ilove737/XS16_CH552T/src/keyMap.h

#ifndef __KEY_MAP_H__
#define __KEY_MAP_H__

#include "CH552.H"
#include "scanKey.h"

// =========================================================================
// 应用场景（纯编号，不再预设语义 ID）
// 所有场景（含主层）统一放入一个大二维数组 sceneMapTable[SCENE_MAX][80]，
// 通过 currentScene 编号偏移定位。每槽 80 字节：
//   [0..15]   应用名称（ASCII，不足补 0，第 16 字节作 0 结尾，最多 15 字符）
//   [16..47]  主层键位（16 键 × 2）
//   [48..79]  该场景专属 Fn 层键位（16 键 × 2）
// =========================================================================
#define SCENE_MAX         6     // 场景槽位总数（编号 0~5）
#define NAME_SIZE         16    // 应用名区长度（字节）
#define KEY_BYTES         32    // 每层键位长度（16 键 × 2 字节）
#define SCENE_MAP_SIZE    80    // 每槽总长度 = NAME_SIZE + KEY_BYTES*2

// 各槽位在数组中的键位区偏移
#define MAP_MAIN_OFF      NAME_SIZE              // 16：主层键位起始
#define MAP_FN_OFF        (NAME_SIZE + KEY_BYTES) // 48：Fn 层键位起始

// 场景指令接收协议（经中断 OUT 端点 3，厂商自定义 Output 报告，Report ID = 2）
// 数据格式：[0]=ReportID(0x02) [1]=SCENE_CMD_MAGIC(0x5C) [2]=场景ID [3..7]=0
#define SCENE_CMD_MAGIC  0x5C

// =========================================================================
// 键位映射大二维数组（编译期固定，__at(0x3600)）
// 6 槽 × 80 字节 = 480 字节，占 0x3600 ~ 0x37DF。
// app 通过扩展后的 Feature Report 可读改写其中任意槽（含应用名与键位）。
// 通用主层键位（deepin 系统快捷键）与 Fn 键位见下方注释。
// =========================================================================
UINT8C __at(0x3600) sceneMapTable[SCENE_MAX][SCENE_MAP_SIZE] = {
    // ---- 槽 0：主层（编号 0，应用名 generic） ----
    {
        /* 应用名 0..15 */
        'g','e','n','e','r','i','c', 0,0,0,0,0,0,0,0,0,
        /* 主层键位 16..47（deepin 系统快捷键，按 keymap_XS16 导出） */
        KEY_MOD_LCTRL|KEY_MOD_LALT, KEY_LEFT,    // Ctrl+Alt+←  切换到左边工作区
        KEY_MOD_LMETA, KEY_S,                    // Win+S       显示工作区
        KEY_MOD_LSHIFT, KEY_SPACE,               // Shift+Space 全局搜索
        KEY_MOD_LCTRL|KEY_MOD_LALT, KEY_RIGHT,   // Ctrl+Alt+→  切换到右边工作区
        KEY_MOD_LALT, KEY_TAB,                   // Alt+Tab     切换窗口
        KEY_MOD_LALT, KEY_GRAVE,                 // Alt+`       切换同类型窗口
        KEY_MOD_LSHIFT|KEY_MOD_LALT, KEY_GRAVE,  // Shift+Alt+` 反向切换同类型窗口
        KEY_MOD_LSHIFT|KEY_MOD_LALT, KEY_TAB,    // Shift+Alt+Tab 反向切换窗口
        KEY_MOD_LALT, KEY_F2,                    // Alt+F2      终端雷神模式
        KEY_MOD_LMETA, KEY_N,                    // Win+N       最小化窗口
        KEY_MOD_LMETA, KEY_UP,                   // Win+↑       最大化窗口
        KEY_MOD_LMETA, KEY_V,                    // Win+V       剪贴板
        KEY_FnX, 0,                              // Fn          切换 Fn 层
        KEY_MOD_LMETA, KEY_LEFT,                 // Win+←       窗口平铺左侧
        KEY_MOD_LMETA, KEY_DOWN,                 // Win+↓       恢复窗口
        KEY_MOD_LMETA, KEY_RIGHT,                // Win+→       窗口平铺右侧
        /* Fn 层键位 48..79（deepin 截图/录屏/图文识别 + 鼠标，按 keymap_XS16 导出） */
        KEY_MOD_LCTRL|KEY_MOD_LALT, KEY_I,       // Ctrl+Alt+I  滚动截图
        KEY_MOD_LCTRL|KEY_MOD_LALT, KEY_A,       // Ctrl+Alt+A  截图
        KEY_MOD_LCTRL, KEY_SYSRQ,                // Ctrl+PrtSc  延时截图
        0, KEY_SYSRQ,                            // PrtSc       全屏截图
        KEY_MOD_LALT, KEY_SYSRQ,                 // Alt+PrtSc   窗口截图
        KEY_MOD_LCTRL|KEY_MOD_LALT, KEY_C,       // Ctrl+Alt+C  图文识别
        KEY_MOD_LCTRL|KEY_MOD_LALT, KEY_R,       // Ctrl+Alt+R  录屏
        KEY_MOD_LMETA, KEY_E,                    // Win+E       文件管理器
        KEY_MOD_LMETA, 0,                        // Win+空      启动器(占位)
        0xFE, MOUSE_LCLICK, 0xFE, MOUSE_UP, 0xFE, MOUSE_RCLICK,
        KEY_FnX, 0,  0xFE, MOUSE_LEFT, 0xFE, MOUSE_DOWN, 0xFE, MOUSE_RIGHT,
    },
    // ---- 槽 1：场景 1（编号 1，应用名 deepin-terminal，终端定制键位） ----
    {
        /* 应用名 0..15 */
        'd','e','e','p','i','n','-','t','e','r','m', 'i','n','a','l',0,
        /* 主层键位 16..47（终端定制，按 keymap_XS16 导出） */
        KEY_MOD_LCTRL|KEY_MOD_LSHIFT, KEY_1,   // Ctrl+Shift+1 切换到标签1
        KEY_MOD_LCTRL|KEY_MOD_LSHIFT, KEY_2,   // Ctrl+Shift+2 切换到标签2
        KEY_MOD_LCTRL, KEY_EQUAL,              // Ctrl+=       放大字号
        KEY_MOD_LCTRL, KEY_MINUS,              // Ctrl+-       缩小字号
        KEY_MOD_LCTRL|KEY_MOD_LSHIFT, KEY_T,   // Ctrl+Shift+T 新建标签页
        KEY_MOD_LCTRL|KEY_MOD_LSHIFT, KEY_TAB, // Ctrl+Shift+Tab 上一个标签页
        KEY_MOD_LCTRL, KEY_TAB,                // Ctrl+Tab     下一个标签页
        KEY_MOD_LALT, KEY_W,                   // Alt+W        关闭标签页
        KEY_MOD_LCTRL|KEY_MOD_LSHIFT, KEY_C,   // Ctrl+Shift+C 复制
        KEY_MOD_LCTRL|KEY_MOD_LSHIFT, KEY_V,   // Ctrl+Shift+V 粘贴
        KEY_MOD_LALT, KEY_DOWN,                // Alt+↓        选择下面工作区
        KEY_MOD_LALT, KEY_Q,                   // Alt+Q        关闭工作区
        KEY_FnX, 0,                            // Fn           切换 Fn 层
        KEY_MOD_LALT, KEY_LEFT,                // Alt+←        选择左边工作区
        KEY_MOD_LALT, KEY_UP,                  // Alt+↑        选择上面工作区
        KEY_MOD_LALT, KEY_RIGHT,               // Alt+→        选择右边工作区
        /* Fn 层键位 48..79（终端分屏/查找/全选 + 鼠标，按 keymap_XS16 导出） */
        KEY_MOD_LCTRL|KEY_MOD_LSHIFT, KEY_J,   // Ctrl+Shift+J 纵向分屏
        KEY_MOD_LCTRL|KEY_MOD_LSHIFT, KEY_H,   // Ctrl+Shift+H 横向分屏
        KEY_MOD_LCTRL|KEY_MOD_LALT, KEY_F,     // Ctrl+Alt+F   查找
        KEY_MOD_LCTRL, KEY_0,                  // Ctrl+0       默认大小
        KEY_MOD_LCTRL|KEY_MOD_LSHIFT, KEY_A,   // Ctrl+Shift+A 全选
        0, KEY_F11,                            // F11          全屏
        KEY_MOD_LCTRL|KEY_MOD_LSHIFT, KEY_W,   // Ctrl+Shift+W 关闭其他标签页
        KEY_MOD_LCTRL|KEY_MOD_LSHIFT, KEY_Q,   // Ctrl+Shift+Q 关闭其他工作区
        0, KEY_F2,                             // F2           重命名标题
        0xFE, MOUSE_LCLICK, 0xFE, MOUSE_UP, 0xFE, MOUSE_RCLICK,
        KEY_FnX, 0,  0xFE, MOUSE_LEFT, 0xFE, MOUSE_DOWN, 0xFE, MOUSE_RIGHT,
    },
    // ---- 槽 2：场景 2（编号 2，应用名 code，VS Code 定制键位） ----
    {
        /* 应用名 0..15 */
        'c','o','d','e', 0,0,0,0,0,0,0,0,0,0,0,0,
        /* 主层键位 16..47（VS Code 编辑优先） */
        KEY_MOD_LCTRL|KEY_MOD_LSHIFT, KEY_P,      // Ctrl+Shift+P   命令面板
        KEY_MOD_LCTRL, KEY_P,                     // Ctrl+P         快速打开文件
        KEY_MOD_LCTRL, KEY_S,                     // Ctrl+S         保存
        KEY_MOD_LCTRL, KEY_GRAVE,                 // Ctrl+`         集成终端
        KEY_MOD_LCTRL, KEY_RIGHTBRACE,            // Ctrl+]         缩进
        KEY_MOD_LCTRL, KEY_LEFTBRACE,             // Ctrl+[         反缩进
        KEY_MOD_LSHIFT|KEY_MOD_LALT, KEY_DOWN,    // Shift+Alt+↓    向下插入光标（列编辑）
        KEY_MOD_LSHIFT|KEY_MOD_LALT, KEY_UP,      // Shift+Alt+↑    向上插入光标（列编辑）
        KEY_MOD_LALT, KEY_DOWN,                   // Alt+↓          下移行
        KEY_MOD_LALT, KEY_UP,                     // Alt+↑          上移行
        KEY_MOD_LCTRL, KEY_D,                     // Ctrl+D         选中下一个匹配
        KEY_MOD_LCTRL|KEY_MOD_LSHIFT, KEY_L,      // Ctrl+Shift+L   全选匹配
        KEY_FnX, 0,                               // Fn             切换 Fn 层
        KEY_MOD_LCTRL, KEY_SLASH,                 // Ctrl+/         行注释
        KEY_MOD_LCTRL|KEY_MOD_LSHIFT, KEY_K,      // Ctrl+Shift+K   删除行
        KEY_MOD_LCTRL, KEY_ENTER,                 // Ctrl+Enter     下方插入行
        /* Fn 层键位 48..79（调试/重构/查找 + 鼠标） */
        0, KEY_F5,                                // F5             启动/继续调试
        0, KEY_F9,                                // F9             切换断点
        0, KEY_F12,                               // F12            转到定义
        0, KEY_F2,                                // F2             重命名符号
        0, KEY_F8,                                // F8             下一个错误
        KEY_MOD_LCTRL, KEY_DOT,                   // Ctrl+.         快速修复
        KEY_MOD_LCTRL|KEY_MOD_LSHIFT, KEY_ENTER,  // Ctrl+Shift+Enter 上方插入行
        KEY_MOD_LCTRL, KEY_F,                     // Ctrl+F         查找
        KEY_MOD_LCTRL, KEY_H,                     // Ctrl+H         替换
        0xFE, MOUSE_LCLICK, 0xFE, MOUSE_UP, 0xFE, MOUSE_RCLICK,
        KEY_FnX, 0,  0xFE, MOUSE_LEFT, 0xFE, MOUSE_DOWN, 0xFE, MOUSE_RIGHT,
    },
    // ---- 槽 3：场景 3（编号 3，应用名 dde-file-manager，deepin 文件管理器定制键位） ----
    {
        /* 应用名 0..15 */
        'f','i','l','e','-','m','a','n','a','g','e','r', 0,0,0,0,
        /* 主层键位 16..47（文件管理器高频操作，按 DEEPIN_FILEMANAGER_SHORTCUTS 挑选） */
        KEY_MOD_LCTRL, KEY_N,                  // Ctrl+N         新建窗口
        KEY_MOD_LCTRL|KEY_MOD_LSHIFT, KEY_N,   // Ctrl+Shift+N   新建文件夹
        KEY_MOD_LCTRL, KEY_T,                  // Ctrl+T         新建标签
        KEY_MOD_LCTRL, KEY_W,                  // Ctrl+W         关闭当前标签
        KEY_MOD_LCTRL, KEY_F,                  // Ctrl+F         搜索
        KEY_MOD_LCTRL, KEY_L,                  // Ctrl+L         地址栏输入
        KEY_MOD_LALT, KEY_LEFT,                // Alt+←          后退
        KEY_MOD_LALT, KEY_RIGHT,               // Alt+→          前进
        KEY_MOD_LCTRL, KEY_UP,                 // Ctrl+↑         返回上一级
        KEY_MOD_LCTRL, KEY_DOWN,               // Ctrl+↓         打开
        KEY_MOD_LCTRL, KEY_A,                  // Ctrl+A         全选
        KEY_MOD_LCTRL, KEY_TAB,                // Ctrl+Tab       切换到下一个标签
        KEY_FnX, 0,                            // Fn             切换 Fn 层
        KEY_MOD_LCTRL, KEY_C,                  // Ctrl+C         复制
        KEY_MOD_LCTRL, KEY_X,                  // Ctrl+X         剪切
        KEY_MOD_LCTRL, KEY_V,                  // Ctrl+V         粘贴
        /* Fn 层键位 48..79（重命名/删除/撤销 + 鼠标） */
        0, KEY_F2,                             // F2             重命名
        0, KEY_DELETE,                         // Delete         删除文件
        KEY_MOD_LSHIFT, KEY_DELETE,            // Shift+Delete   彻底删除
        KEY_MOD_LCTRL|KEY_MOD_LSHIFT, KEY_C,   // Ctrl+Shift+C   复制文件地址
        KEY_MOD_LSHIFT, KEY_T,                 // Shift+T        在终端中打开
        KEY_MOD_LCTRL, KEY_H,                  // Ctrl+H         隐藏文件
        KEY_MOD_LCTRL, KEY_Z,                  // Ctrl+Z         撤销
        KEY_MOD_LCTRL, KEY_Y,                  // Ctrl+Y         重做
        KEY_MOD_LCTRL|KEY_MOD_LSHIFT, KEY_TAB, // Ctrl+Shift+Tab 切换到上一个标签
        0xFE, MOUSE_LCLICK, 0xFE, MOUSE_UP, 0xFE, MOUSE_RCLICK,
        KEY_FnX, 0,  0xFE, MOUSE_LEFT, 0xFE, MOUSE_DOWN, 0xFE, MOUSE_RIGHT,
    },
    // ---- 槽 4：预留场景（编号 4，应用名为空，沿用通用键位） ----
    {
        /* 应用名 0..15 */
        0,0,0,0,0,0,0,0,0,0,0,0,0,0,0,0,
        /* 主层键位 16..47（通用） */
        KEY_MOD_LCTRL|KEY_MOD_LALT, KEY_T,
        0, KEY_LEFTMETA,
        KEY_MOD_LCTRL|KEY_MOD_LALT, KEY_A,
        KEY_MOD_LCTRL|KEY_MOD_LALT, KEY_R,
        KEY_MOD_LALT, KEY_TAB,
        KEY_MOD_LMETA, KEY_D,
        KEY_MOD_LMETA, KEY_E,
        KEY_MOD_LMETA, KEY_L,
        KEY_MOD_LALT, KEY_F4,
        KEY_MOD_LMETA, KEY_S,
        KEY_MOD_LMETA, KEY_UP,
        KEY_MOD_LMETA, KEY_DOWN,
        KEY_FnX, 0,
        KEY_MOD_LCTRL|KEY_MOD_LALT, KEY_ESC,
        KEY_MOD_LCTRL|KEY_MOD_LALT, KEY_DELETE,
        KEY_MOD_LMETA, KEY_P,
        /* Fn 层键位 48..79（通用功能键） */
        0, KEY_ESC,  0, KEY_F1,  0, KEY_F2,  0, KEY_F3,
        0, KEY_TAB,  0, KEY_F11, 0, KEY_F12, 0, KEY_E,
        0, KEY_CAPSLOCK, 0xFE, MOUSE_LCLICK, 0xFE, MOUSE_UP, 0xFE, MOUSE_RCLICK,
        KEY_FnX, 0,  0xFE, MOUSE_LEFT, 0xFE, MOUSE_DOWN, 0xFE, MOUSE_RIGHT,
    },
    // ---- 槽 5：预留场景（编号 5，应用名为空，沿用通用键位） ----
    {
        /* 应用名 0..15 */
        0,0,0,0,0,0,0,0,0,0,0,0,0,0,0,0,
        /* 主层键位 16..47（通用） */
        KEY_MOD_LCTRL|KEY_MOD_LALT, KEY_T,
        0, KEY_LEFTMETA,
        KEY_MOD_LCTRL|KEY_MOD_LALT, KEY_A,
        KEY_MOD_LCTRL|KEY_MOD_LALT, KEY_R,
        KEY_MOD_LALT, KEY_TAB,
        KEY_MOD_LMETA, KEY_D,
        KEY_MOD_LMETA, KEY_E,
        KEY_MOD_LMETA, KEY_L,
        KEY_MOD_LALT, KEY_F4,
        KEY_MOD_LMETA, KEY_S,
        KEY_MOD_LMETA, KEY_UP,
        KEY_MOD_LMETA, KEY_DOWN,
        KEY_FnX, 0,
        KEY_MOD_LCTRL|KEY_MOD_LALT, KEY_ESC,
        KEY_MOD_LCTRL|KEY_MOD_LALT, KEY_DELETE,
        KEY_MOD_LMETA, KEY_P,
        /* Fn 层键位 48..79（通用功能键） */
        0, KEY_ESC,  0, KEY_F1,  0, KEY_F2,  0, KEY_F3,
        0, KEY_TAB,  0, KEY_F11, 0, KEY_F12, 0, KEY_E,
        0, KEY_CAPSLOCK, 0xFE, MOUSE_LCLICK, 0xFE, MOUSE_UP, 0xFE, MOUSE_RCLICK,
        KEY_FnX, 0,  0xFE, MOUSE_LEFT, 0xFE, MOUSE_DOWN, 0xFE, MOUSE_RIGHT,
    },
};

#endif // KEY_MAP
