ilove737/XS16_CH552T/tools/app/src-tauri/src/lib.rs

// Prevents additional console window on Windows in release, DO NOT REMOVE!!
#![cfg_attr(not(debug_assertions), windows_subsystem = "windows")]

use std::collections::HashMap;
use std::sync::atomic::{AtomicBool, Ordering};
use std::sync::Mutex;
use std::thread;
#[cfg(target_os = "linux")]
use std::time::Duration;

use hidapi::HidApi;
use hidapi::HidDevice;
use serde::Serialize;
use tauri::{
    menu::{Menu, MenuItem, MenuEvent},
    tray::{MouseButton, MouseButtonState, TrayIconBuilder, TrayIconEvent},
    Manager, RunEvent, State, WindowEvent,
};
#[cfg(target_os = "linux")]
use raw_window_handle::{HasWindowHandle, RawWindowHandle};

const VID: u16 = 0x4c58;
const PID: u16 = 0x5310;
const KEYMAP_LEN: usize = 480; // 6 scenes * 80 bytes（与固件 sceneMapTable[SCENE_MAX][SCENE_MAP_SIZE] 一致）
const KEYMAP_REPORT_ID: u8 = 0x01; // 固件 KEYMAP_REPORT_ID，与报表描述符一致
// 以下场景相关常量仅 Linux 前台检测 (match_app_to_scene) 使用
#[cfg(target_os = "linux")]
const SCENE_MAX: usize = 6; // 槽 0 为主层，1..5 为场景（与固件 keyMap.h SCENE_MAX 一致）
#[cfg(target_os = "linux")]
const SCENE_MAP_SIZE: usize = 80; // 每槽总长度 = 16 应用名 + 32 主层 + 32 Fn 层（与固件 SCENE_MAP_SIZE 一致）
#[cfg(target_os = "linux")]
const SCENE_NAME_LEN: usize = 16; // 每个槽前 16 字节为应用名

// 轮询线程所需的可共享状态（用 Arc 包裹，可独立 clone 给线程）
pub struct PollShared {
    pub keymap: Mutex<Vec<u8>>,    // 480 字节真相源（方案 A）
    pub last_scene: Mutex<i32>,    // 自动轮询去重
    pub last_app: Mutex<String>,   // 激活应用日志去重
    pub running: AtomicBool,       // 线程退出信号
}

impl Default for PollShared {
    fn default() -> Self {
        PollShared {
            keymap: Mutex::new(vec![0u8; KEYMAP_LEN]),
            last_scene: Mutex::new(-1),
            last_app: Mutex::new(String::new()),
            running: AtomicBool::new(false),
        }
    }
}

#[derive(Default)]
pub struct AppState {
    pub devices: Mutex<HashMap<String, HidDevice>>, // path -> device
    pub last_active_app: Mutex<String>,             // active_app 日志去重
    pub poll: std::sync::Arc<PollShared>,           // 轮询线程共享状态
    pub auto_poll: Mutex<Option<thread::JoinHandle<()>>>, // 轮询线程句柄
}

#[derive(Serialize, Clone)]
struct DeviceInfo {
    path: String,
    product: String,
    serial: String,
}

#[derive(Serialize, Clone)]
struct ActiveApp {
    app_name: String, // WM_CLASS 实例名（如 unknown、xs16keymap）
    title: String,    // 窗口标题（_NET_WM_NAME / WM_NAME）
    pid: u32,         // 真实窗口 PID（_NET_WM_PID）
    self_pid: u32,
}

#[derive(Serialize, Clone)]
struct WindowInfo {
    id: u32,          // X11 窗口 ID
    app_name: String, // WM_CLASS 实例名
    title: String,    // 窗口标题
    pid: u32,         // 窗口 PID
}

#[derive(Serialize)]
struct PollStatus {
    app_name: String,
    title: String,
    pid: u32,
    matched_scene: i32,
}

#[tauri::command]
fn list_devices(state: State<AppState>) -> Result<Vec<DeviceInfo>, String> {
    let api = HidApi::new().map_err(|e| e.to_string())?;
    let mut out = Vec::new();
    // 同一台键盘固件暴露了多个 HID 接口（Keyboard + Mouse），
    // 每个接口 VID:PID 相同，只取第一个匹配接口（interface 0，即键盘通信接口），
    // 避免前端把一台物理设备显示成多个。
    for d in api.device_list() {
        if d.vendor_id() == VID && d.product_id() == PID {
            let serial = d.serial_number().unwrap_or("").to_string();
            let path = d.path().to_string_lossy().to_string();
            let product = d.product_string().unwrap_or("XS16 Keyboard").to_string();
            if state.devices.lock().unwrap().contains_key(&path) {
                continue; // 已经打开的不重复列出
            }
            out.push(DeviceInfo {
                path,
                product,
                serial,
            });
            break; // 单设备：只取第一个接口，跳过 Mouse 等辅助接口
        }
    }
    Ok(out)
}

#[tauri::command]
fn open_device(path: String, state: State<AppState>) -> Result<(), String> {
    let api = HidApi::new().map_err(|e| e.to_string())?;
    let dev = api.open_path(&std::ffi::CString::new(path.as_bytes()).map_err(|e| e.to_string())?)
        .map_err(|e| e.to_string())?;
    state.devices.lock().unwrap().insert(path, dev);
    Ok(())
}

#[tauri::command]
fn close_device(path: String, state: State<AppState>) -> Result<(), String> {
    if let Some(dev) = state.devices.lock().unwrap().remove(&path) {
        drop(dev);
    }
    Ok(())
}

// 安装 udev 规则，使当前用户无需 root 权限即可访问 XS16 键盘
#[tauri::command]
#[cfg(target_os = "linux")]
fn install_udev_rule() -> Result<String, String> {
    use std::fs;
    use std::process::Command;

    let rule_path = "/etc/udev/rules.d/99-xs16.rules";
    let rule_content = r#"SUBSYSTEM=="hidraw", ATTRS{idVendor}=="4c58", ATTRS{idProduct}=="5310", MODE="0666""#;

    // 检查规则文件是否已存在且内容正确
    if let Ok(existing) = fs::read_to_string(rule_path) {
        if existing.contains("4c58") && existing.contains("5310") {
            // 规则已存在，只需 reload
            let status = Command::new("pkexec")
                .args(["udevadm", "control", "--reload-rules"])
                .status()
                .map_err(|e| format!("执行 pkexec 失败: {}", e))?;
            if status.success() {
                // 同时触发 udev 重新加载设备
                let _ = Command::new("pkexec")
                    .args(["udevadm", "trigger"])
                    .status();
                return Ok("udev 规则已存在，已重新加载".to_string());
            } else {
                return Err("用户取消了授权或授权失败".to_string());
            }
        }
    }

    // 通过 pkexec 执行写入规则 + reload（pkexec 会弹出图形密码对话框）
    let script = format!(
        "echo '{}' > {} && udevadm control --reload-rules && udevadm trigger",
        rule_content, rule_path
    );
    let status = Command::new("pkexec")
        .args(["bash", "-c", &script])
        .status()
        .map_err(|e| format!("执行 pkexec 失败: {}", e))?;

    if status.success() {
        Ok("udev 规则已安装成功".to_string())
    } else {
        Err("用户取消了授权或授权失败".to_string())
    }
}

// 非 Linux 平台无需 udev 规则
#[tauri::command]
#[cfg(not(target_os = "linux"))]
fn install_udev_rule() -> Result<String, String> {
    Err("udev 规则仅在 Linux 上需要".to_string())
}

// 读取特征报告 0x01: 键位数据（一次 GetReport 回传整条 481 字节）
#[tauri::command]
fn read_keymap(state: State<AppState>) -> Result<Vec<u8>, String> {
    println!("{} [read_keymap] 开始读取设备键位", log_prefix());
    let api = HidApi::new().map_err(|e| e.to_string())?;
    let dev = open_first(&api, &state)?;
    // 固件 GetReport(case 0x01) 会主动把 KeymapBuf 内容回传，无需先发 SetReport。
    // 注意：若先发 send_feature_report 会被固件当成 SetReport，收满全 0 后写 Flash 清零！
    println!("{} [read_keymap] 已打开设备，直接 GetReport 0x01 回读整条键位", log_prefix());
    // report id = 0x01（与固件 KEYMAP_REPORT_ID 一致），buffer = 481 字节（1 report id + 480 数据）
    let mut buf = [0u8; KEYMAP_LEN + 1];
    buf[0] = KEYMAP_REPORT_ID;
    // 一次 GetReport 即可拿全 481 字节（含 report id），hidapi 内部处理控制传输多包
    let n = dev.get_feature_report(&mut buf).map_err(|e| e.to_string())?;
    println!("{} [read_keymap] 回读成功，实际字节数={}（含 report id）", log_prefix(), n);
    // get_feature_report 返回的 n 包含 report id 字节（通常为 481）
    let data = if n > 1 { buf[1..n].to_vec() } else { Vec::new() };
    println!("{} [read_keymap] 键位数据长度={} 字节", log_prefix(), data.len());
    // 同步真相源（方案 A）
    if data.len() >= KEYMAP_LEN {
        *state.poll.keymap.lock().unwrap() = data[..KEYMAP_LEN].to_vec();
        println!("{} [read_keymap] 已同步真相源（{} 字节）", log_prefix(), KEYMAP_LEN);
    } else {
        println!("{} [read_keymap] 警告：回读长度 {} < {}，未同步真相源", log_prefix(), data.len(), KEYMAP_LEN);
    }
    Ok(data)
}

// 写入特征报告 0x01: 键位数据 (落盘 Flash)
#[tauri::command]
fn write_keymap(state: State<AppState>, data: Vec<u8>) -> Result<(), String> {
    println!("{} [write_keymap] 开始写入设备，入参长度={} 字节", log_prefix(), data.len());
    let api = HidApi::new().map_err(|e| e.to_string())?;
    let dev = open_first(&api, &state)?;
    println!("{} [write_keymap] 已打开设备，准备发送 feature report 0x01", log_prefix());
    let mut buf = [0u8; KEYMAP_LEN + 1];
    buf[0] = KEYMAP_REPORT_ID; // 0x01
    let len = data.len().min(KEYMAP_LEN);
    buf[1..1 + len].copy_from_slice(&data[..len]);
    dev.send_feature_report(&buf).map_err(|e| e.to_string())?;
    println!("{} [write_keymap] 已发送 feature report，实际写入 {} 字节", log_prefix(), len);
    // 同步真相源（方案 A）
    *state.poll.keymap.lock().unwrap() = data[..len].to_vec();
    println!("{} [write_keymap] 已同步真相源（{} 字节）", log_prefix(), len);
    Ok(())
}

// 把前端编辑后的键位写入真相源（不落盘，落盘由 write_keymap 负责）
#[tauri::command]
fn set_keymap(state: State<AppState>, data: Vec<u8>) -> Result<(), String> {
    let mut km = state.poll.keymap.lock().unwrap();
    if data.len() >= KEYMAP_LEN {
        *km = data[..KEYMAP_LEN].to_vec();
    } else {
        // 长度不足则补零
        let mut padded = data.clone();
        padded.resize(KEYMAP_LEN, 0);
        *km = padded;
    }
    Ok(())
}

// 返回真相源当前 480 字节，供前端渲染
#[tauri::command]
fn get_keymap(state: State<AppState>) -> Result<Vec<u8>, String> {
    let km = state.poll.keymap.lock().unwrap();
    Ok(km.clone())
}

// 抽取场景下发内部实现，供命令与轮询线程复用
fn send_scene_impl(scene_id: u8) -> Result<(), String> {
    let api = HidApi::new().map_err(|e| e.to_string())?;
    let dev = api
        .open(VID, PID)
        .map_err(|e| format!("打开设备失败: {}", e))?;
    // 协议（与固件 CompositeKM.C OUT 端点 3 解析 + VendorRepDesc 一致）：
    // [0]=ReportID(0x02) [1]=SCENE_CMD_MAGIC(0x5C) [2]=场景ID [3..8]=0
    let mut buf = [0u8; 8]; // 1 ReportID + 8 字节载荷（Report Count=8）
    buf[0] = 0x02;     // Report ID（与 VendorRepDesc 0x85,0x02 一致）
    buf[1] = 0x5C;     // SCENE_CMD_MAGIC（固件校验 Ep3Buffer[1]）
    buf[2] = scene_id; // 场景 ID（固件读 Ep3Buffer[2]）
    dev.write(&buf).map_err(|e| e.to_string())?;
    Ok(())
}

#[tauri::command]
fn send_scene(scene_id: u8, state: State<AppState>) -> Result<(), String> {
    let r = send_scene_impl(scene_id);
    if r.is_ok() {
        *state.poll.last_scene.lock().unwrap() = scene_id as i32;
    }
    r
}

// X11 前台应用检测（纯 Rust 实现，仅 Linux）
#[cfg(target_os = "linux")]
fn active_app_impl() -> Result<ActiveApp, String> {
    use x11rb::connection::Connection;
    use x11rb::protocol::xproto::ConnectionExt;
    use x11rb::xcb_ffi::XCBConnection;

    let (conn, _) = XCBConnection::connect(None).map_err(|e| format!("X11 connect: {}", e))?;
    let setup = conn.setup();
    let root = setup.roots[0].root;

    use x11rb::protocol::xproto::AtomEnum;

    // 获取真正的"前台/激活窗口"（_NET_ACTIVE_WINDOW 指向当前聚焦的顶层窗口，
    // 而非 _NET_CLIENT_LIST 的最后一个客户窗口，后者顺序由 WM 决定、不等于前台窗口）
    let net_active = intern_atom(&conn, b"_NET_ACTIVE_WINDOW")?;
    let reply = conn
        .get_property(false, root, net_active, AtomEnum::ANY, 0, 32)
        .map_err(|e| e.to_string())?
        .reply()
        .map_err(|e| e.to_string())?;
    let windows: Vec<u32> = reply
        .value
        .chunks_exact(4)
        .map(|c| u32::from_ne_bytes([c[0], c[1], c[2], c[3]]))
        .collect();
    let active = *windows.first().unwrap_or(&0);

    if active == 0 {
        // 锁屏 / 无前台窗口时 _NET_ACTIVE_WINDOW 为空，属正常现象，
        // 语义降级为“当前无前台应用”，返回空 ActiveApp 而非报错刷屏。
        // 真正的 X11 连接/读取错误仍以上面各 ? 的 Err 形式抛出。
        return Ok(ActiveApp {
            app_name: String::new(),
            title: String::new(),
            pid: 0,
            self_pid: std::process::id(),
        });
    }

    // 使用辅助函数读取窗口信息
    let info = read_window_info(&conn, active)?;
    let self_pid = std::process::id();
    Ok(ActiveApp {
        app_name: info.app_name,
        title: info.title,
        pid: info.pid,
        self_pid,
    })
}

// 辅助函数：读取指定 X11 窗口的信息（WM_CLASS、_NET_WM_NAME、_NET_WM_PID）
#[cfg(target_os = "linux")]
fn read_window_info<C: x11rb::connection::Connection>(
    conn: &C,
    window_id: u32,
) -> Result<WindowInfo, String> {
    use x11rb::protocol::xproto::ConnectionExt;

    // name = WM_CLASS 实例名（第一个字符串）。WM_CLASS 形如 "instance\0class\0"。
    let wm_class = intern_atom(conn, b"WM_CLASS")?;
    let wm_class_reply = conn
        .get_property(false, window_id, wm_class, x11rb::protocol::xproto::AtomEnum::STRING, 0, 1024)
        .map_err(|e| e.to_string())?
        .reply()
        .map_err(|e| e.to_string())?;
    let app_name = {
        let raw = String::from_utf8_lossy(&wm_class_reply.value);
        let parts: Vec<&str> = raw.split('\0').collect();
        // 第一个非空段为 instance，第二个为 class
        parts
            .iter()
            .find(|s| !s.is_empty())
            .map(|s| s.to_string())
            .unwrap_or_default()
    };

    // title = 窗口标题：优先 _NET_WM_NAME，回退 WM_NAME
    let net_wm_name = intern_atom(conn, b"_NET_WM_NAME")?;
    let utf8 = intern_atom(conn, b"UTF8_STRING")?;
    let name_reply = conn
        .get_property(false, window_id, net_wm_name, utf8, 0, 1024)
        .map_err(|e| e.to_string())?
        .reply()
        .map_err(|e| e.to_string())?;
    let title = if name_reply.value_len > 0 {
        String::from_utf8_lossy(&name_reply.value).to_string()
    } else {
        let wm_name = conn
            .get_property(false, window_id, x11rb::protocol::xproto::AtomEnum::WM_NAME, x11rb::protocol::xproto::AtomEnum::STRING, 0, 1024)
            .map_err(|e| e.to_string())?
            .reply()
            .map_err(|e| e.to_string())?;
        String::from_utf8_lossy(&wm_name.value).to_string()
    };

    // pid = 真实窗口 PID（_NET_WM_PID，CARDINAL，4 字节）
    let net_wm_pid = intern_atom(conn, b"_NET_WM_PID")?;
    let pid_reply = conn
        .get_property(false, window_id, net_wm_pid, x11rb::protocol::xproto::AtomEnum::CARDINAL, 0, 4)
        .map_err(|e| e.to_string())?
        .reply()
        .map_err(|e| e.to_string())?;
    let pid = if pid_reply.value.len() >= 4 {
        u32::from_ne_bytes([
            pid_reply.value[0],
            pid_reply.value[1],
            pid_reply.value[2],
            pid_reply.value[3],
        ])
    } else {
        0
    };

    Ok(WindowInfo {
        id: window_id,
        app_name,
        title,
        pid,
    })
}

#[cfg(target_os = "linux")]
fn intern_atom<C: x11rb::connection::Connection>(
    conn: &C,
    name: &[u8],
) -> Result<x11rb::protocol::xproto::Atom, String> {
    use x11rb::protocol::xproto::ConnectionExt;
    let reply = conn
        .intern_atom(false, name)
        .map_err(|e| e.to_string())?
        .reply()
        .map_err(|e| e.to_string())?;
    Ok(reply.atom)
}

// 获取所有打开的窗口列表（仅 Linux，基于 _NET_CLIENT_LIST）
#[cfg(target_os = "linux")]
fn list_windows_impl() -> Result<Vec<WindowInfo>, String> {
    use x11rb::connection::Connection;
    use x11rb::protocol::xproto::ConnectionExt;
    use x11rb::xcb_ffi::XCBConnection;

    let (conn, _) = XCBConnection::connect(None).map_err(|e| format!("X11 connect: {}", e))?;
    let setup = conn.setup();
    let root = setup.roots[0].root;

    use x11rb::protocol::xproto::AtomEnum;

    // 读取 _NET_CLIENT_LIST（窗口管理器维护的已管理窗口列表）
    let client_list = intern_atom(&conn, b"_NET_CLIENT_LIST")?;
    let reply = conn
        .get_property(false, root, client_list, AtomEnum::WINDOW, 0, u32::MAX)
        .map_err(|e| e.to_string())?
        .reply()
        .map_err(|e| e.to_string())?;

    let window_ids: Vec<u32> = reply
        .value
        .chunks_exact(4)
        .map(|c| u32::from_ne_bytes([c[0], c[1], c[2], c[3]]))
        .collect();

    let mut windows = Vec::new();
    for wid in window_ids {
        if wid == 0 {
            continue;
        }
        // 读取每个窗口的信息
        if let Ok(info) = read_window_info(&conn, wid) {
            // 只添加有应用名的窗口（过滤掉装饰窗口等）
            if !info.app_name.is_empty() {
                windows.push(info);
            }
        }
    }
    Ok(windows)
}

#[tauri::command]
fn active_app(state: State<AppState>) -> Result<ActiveApp, String> {
    #[cfg(target_os = "linux")]
    {
        let app = active_app_impl()?;
        let mut last = state.last_active_app.lock().unwrap();
        if *last != app.app_name {
            println!("{} [active_app] app={} pid={} title=\"{}\"",
                log_prefix(), app.app_name, app.pid, app.title);
            *last = app.app_name.clone();
        }
        Ok(app)
    }
    #[cfg(not(target_os = "linux"))]
    {
        let _ = &state;
        Err("active_app 仅在 Linux (X11) 上支持".to_string())
    }
}

// 返回所有打开的窗口列表，供前端场景名下拉选择
#[tauri::command]
fn list_windows(state: State<AppState>) -> Result<Vec<WindowInfo>, String> {
    #[cfg(target_os = "linux")]
    {
        let _ = &state;
        list_windows_impl()
    }
    #[cfg(not(target_os = "linux"))]
    {
        let _ = &state;
        Err("list_windows 仅在 Linux (X11) 上支持".to_string())
    }
}

// 从真相源 480 字节中匹配前台 app 名到场景槽
// 每个槽前 16 字节为应用名（遇 \0 截断，按 ; 拆别名，小写化）
// 返回命中槽号（1..SCENE_MAX），未命中返回 0（仅 Linux 前台检测使用）
#[cfg(target_os = "linux")]
fn match_app_to_scene(keymap: &[u8], app_name: &str) -> i32 {
    // 真相源长度不足一个完整槽时无法匹配
    if keymap.len() < KEYMAP_LEN {
        return 0;
    }
    // 前台 app 名统一小写，匹配忽略大小写
    let app_lower = app_name.to_lowercase();
    // 空名直接判未命中
    if app_lower.is_empty() {
        return 0;
    }
    let slot_size = SCENE_MAP_SIZE; // 80：每槽 = 16 应用名 + 32 主层 + 32 Fn 层
    // 槽 0 为主层（不用于匹配），从 1..SCENE_MAX 遍历各场景槽
    for scene in 1..SCENE_MAX {
        // 各场景槽在真相源中的起始偏移
        let base = scene * slot_size;
        // 槽前 SCENE_NAME_LEN(16) 字节为该槽配置的应用名区域
        let name_bytes = &keymap[base..base + SCENE_NAME_LEN];
        // 解析为 UTF-8 失败则该槽不可读，跳过
        let name = match std::str::from_utf8(name_bytes) {
            Ok(s) => s,
            Err(_) => continue,
        };
        // 应用名以 \0 结尾截断，取首个字符串并去首尾空白
        let name = name.split('\0').next().unwrap_or("").trim();
        // 空名（未配置）的槽跳过
        if name.is_empty() {
            continue;
        }
        // 同一槽可配多个别名，用 ; 分隔，逐个匹配
        for alias in name.split(';') {
            // 别名统一小写、去空白；空别名跳过
            let alias = alias.trim().to_lowercase();
            if alias.is_empty() {
                continue;
            }
            // 精确相等，或前台应用名包含别名（子串匹配）即视为命中
            if app_lower == alias || app_lower.contains(&alias) {
                return scene as i32;
            }
        }
    }
    0
}

// 轮询线程：每 1s 检测前台应用，匹配到场景且变化才下发（仅 Linux）
#[cfg(target_os = "linux")]
fn poll_loop(shared: std::sync::Arc<PollShared>) {
    loop {
        if !shared.running.load(Ordering::SeqCst) {
            break;
        }
        thread::sleep(Duration::from_secs(1));
        if !shared.running.load(Ordering::SeqCst) {
            break;
        }
        let app = match active_app_impl() {
            Ok(a) => a,
            Err(e) => {
                println!("{} [poll_loop] active_app failed: {}", log_prefix(), e);
                continue;
            }
        };
        // 激活应用（name）变化时打印一行，避免每秒刷屏
        let mut last_app = shared.last_app.lock().unwrap();
        if *last_app != app.app_name {
            println!("{} [poll_loop] app={} pid={} title=\"{}\"",
                log_prefix(), app.app_name, app.pid, app.title);
            *last_app = app.app_name.clone();
        }
        let km = shared.keymap.lock().unwrap().clone();
        // 0 = 未匹配 → 切回 generic(槽0)；命中 → 下发对应场景号
        let scene = match_app_to_scene(&km, &app.app_name);
        let mut last = shared.last_scene.lock().unwrap();
        if scene != *last {
            // 变化才发（去重）：命中下发场景号，未命中下发 0(generic)，避免每秒重复下发刷屏
            let _ = send_scene_impl(scene as u8);
            println!("{} [poll_loop] app={} -> scene={} ({})",
                log_prefix(), app.app_name, scene,
                if scene == 0 { "generic" } else { "matched" });
            *last = scene;
        }
    }
}

#[tauri::command]
#[cfg(target_os = "linux")]
fn start_auto_poll(state: State<AppState>) -> Result<(), String> {
    let mut handle = state.auto_poll.lock().unwrap();
    if handle.is_some() {
        return Ok(()); // 已在运行
    }
    state.poll.running.store(true, Ordering::SeqCst);
    let sh = std::sync::Arc::clone(&state.poll);
    let h = thread::spawn(move || poll_loop(sh));
    *handle = Some(h);
    Ok(())
}

// 非 Linux 平台无 X11 前台检测，自动轮询无意义，直接返回成功
#[tauri::command]
#[cfg(not(target_os = "linux"))]
fn start_auto_poll(_state: State<AppState>) -> Result<(), String> {
    Ok(())
}

#[tauri::command]
#[cfg(target_os = "linux")]
fn stop_auto_poll(state: State<AppState>) -> Result<(), String> {
    let mut handle = state.auto_poll.lock().unwrap();
    if handle.is_none() {
        return Ok(());
    }
    state.poll.running.store(false, Ordering::SeqCst);
    if let Some(h) = handle.take() {
        let _ = h.join();
    }
    Ok(())
}

// 非 Linux 平台无后台轮询线程，直接返回成功
#[tauri::command]
#[cfg(not(target_os = "linux"))]
fn stop_auto_poll(_state: State<AppState>) -> Result<(), String> {
    Ok(())
}

// 返回当前前台应用 + 已匹配场景，供前端"当前应用"栏展示
#[tauri::command]
fn get_poll_status(state: State<AppState>) -> Result<PollStatus, String> {
    #[cfg(target_os = "linux")]
    {
        let app = match active_app_impl() {
            Ok(a) => a,
            Err(e) => {
                // 检测失败也要记录，便于排查 X11 / Wayland / 权限问题
                println!("{} [get_poll_status] active_app failed: {}", log_prefix(), e);
                return Err(e);
            }
        };
        let km = state.poll.keymap.lock().unwrap().clone();
        let matched_scene = match_app_to_scene(&km, &app.app_name);
        Ok(PollStatus {
            app_name: app.app_name,
            title: app.title,
            pid: app.pid,
            matched_scene,
        })
    }
    #[cfg(not(target_os = "linux"))]
    {
        let _ = &state;
        Err("get_poll_status 仅在 Linux (X11) 上支持".to_string())
    }
}

// 创建系统托盘：图标 + 右键菜单（显示窗口 / 退出）+ 左键点击恢复窗口
fn setup_tray(app: &tauri::AppHandle) -> tauri::Result<()> {
    let icon_bytes = include_bytes!("../icons/icon.png");
    let icon = tauri::image::Image::from_bytes(icon_bytes)?;

    let show = MenuItem::with_id(app, "show", "显示窗口", true, None::<&str>)?;
    let quit = MenuItem::with_id(app, "quit", "退出", true, None::<&str>)?;
    let menu = Menu::with_items(app, &[&show, &quit])?;

    let _tray = TrayIconBuilder::with_id("main-tray")
        .icon(icon)
        .tooltip("XS16 键位映射编辑器")
        .menu(&menu)
        .on_menu_event(|app: &tauri::AppHandle, event: MenuEvent| match event.id().as_ref() {
            "show" => {
                if let Some(w) = app.get_webview_window("main") {
                    let _ = w.show();
                    let _ = w.unminimize();
                    let _ = w.set_focus();
                }
            }
            "quit" => {
                app.exit(0);
            }
            _ => {}
        })
        .on_tray_icon_event(|tray: &tauri::tray::TrayIcon, event: TrayIconEvent| {
            // 左键单击 / 双击托盘图标：恢复并聚焦窗口
            if let TrayIconEvent::Click {
                button: MouseButton::Left,
                button_state: MouseButtonState::Up,
                ..
            } = event
            {
                if let Some(w) = tray.app_handle().get_webview_window("main") {
                    let _ = w.show();
                    let _ = w.unminimize();
                    let _ = w.set_focus();
                }
            }
        })
        .build(app)?;
    Ok(())
}

/// 在 X11 (Linux) 上，Tauri v2 的 `set_icon` 不会把图标写入窗口的 `_NET_WM_ICON`
/// 属性，导致 DDE/GNOME 任务栏显示默认图标。这里直接用 X11 协议把 PNG 图标写入
/// `_NET_WM_ICON`，确保任务栏显示应用图标。非 X11 平台直接跳过。
#[cfg(target_os = "linux")]
fn set_x11_window_icon(window: &tauri::WebviewWindow) -> Option<()> {
    use x11rb::connection::Connection;
    use x11rb::protocol::xproto::{ConnectionExt as XProtoExt, PropMode};
    use x11rb::wrapper::ConnectionExt;

    // 1. 取 X11 原生窗口 ID
    let raw = window.window_handle().ok()?;
    let xid: u32 = match raw.as_ref() {
        RawWindowHandle::Xlib(h) => h.window as u32,
        _ => return None,
    };
    if xid == 0 {
        return None;
    }

    // 2. 连接 X server（同用户进程可修改任意窗口属性）
    let (conn, _screen) = x11rb::connect(None).ok()?;

    // 3. 解码 PNG -> RGBA 像素
    let icon_bytes = include_bytes!("../icons/icon.png");
    let img = tauri::image::Image::from_bytes(icon_bytes).ok()?;
    let w = img.width();
    let h = img.height();
    let rgba = img.rgba(); // &[u8], 长度 = w*h*4 (RGBA)

    // 4. 构造 _NET_WM_ICON 数据：[w, h, ARGB...]，ARGB = 0xAARRGGBB
    let mut data: Vec<u32> = Vec::with_capacity(2 + w as usize * h as usize);
    data.push(w);
    data.push(h);
    for px in rgba.chunks_exact(4) {
        let r = px[0] as u32;
        let g = px[1] as u32;
        let b = px[2] as u32;
        let a = px[3] as u32;
        data.push((a << 24) | (r << 16) | (g << 8) | b);
    }

    // 5. 写入属性（CARDINAL 预定义 atom = 6）
    let atom = conn
        .intern_atom(false, b"_NET_WM_ICON")
        .ok()?
        .reply()
        .ok()?
        .atom;
    if atom == 0 {
        return None;
    }
    conn.change_property32(PropMode::REPLACE, xid, atom, 6u32, &data)
        .ok()?;
    conn.flush().ok()?;
    Some(())
}

fn open_first(api: &HidApi, _state: &State<AppState>) -> Result<HidDevice, String> {
    let dev = api
        .open(VID, PID)
        .map_err(|e| format!("未找到 XS16 设备 (VID:PID = {:04x}:{:04x}): {}", VID, PID, e))?;
    Ok(dev)
}

// 日志统一前缀：[时间戳]
fn log_prefix() -> String {
    format!(
        "[{}]",
        chrono::Local::now().format("%y%m%d %H:%M:%S%.3f")
    )
}

#[cfg_attr(mobile, tauri::mobile_entry_point)]
pub fn run() {
    tauri::Builder::default()
        .plugin(tauri_plugin_shell::init())
        .plugin(tauri_plugin_dialog::init())
        .plugin(tauri_plugin_fs::init())
        .manage(AppState::default())
        .setup(|app| {
            // 创建系统托盘（图标 + 菜单 + 托盘点击恢复窗口）
            setup_tray(app.handle())?;

            // 给主窗口设置图标，确保任务栏/标题栏显示应用图标
            if let Some(window) = app.get_webview_window("main") {
                #[cfg(target_os = "linux")]
                let _ = set_x11_window_icon(&window);
                #[cfg(not(target_os = "linux"))]
                {
                    let icon_bytes = include_bytes!("../icons/icon.png");
                    if let Ok(img) = tauri::image::Image::from_bytes(icon_bytes) {
                        let _ = window.set_icon(img);
                    }
                }
            }
            Ok(())
        })
        .invoke_handler(tauri::generate_handler![
            list_devices,
            open_device,
            close_device,
            install_udev_rule,
            read_keymap,
            write_keymap,
            set_keymap,
            get_keymap,
            send_scene,
            active_app,
            list_windows,
            start_auto_poll,
            stop_auto_poll,
            get_poll_status,
        ])
        .on_window_event(|window, event| {
            // 拦截窗口关闭请求：隐藏到系统托盘而非退出进程
            if let WindowEvent::CloseRequested { api, .. } = event {
                api.prevent_close();
                let _ = window.hide();
            }
        })
        .build(tauri::generate_context!())
        .expect("error while building tauri application")
        .run(|app, event| {
            // 真正退出前停止自动轮询线程（包括托盘"退出"触发的退出）
            if let RunEvent::ExitRequested { .. } = event {
                stop_poll_on_exit(app);
            }
        });
}

// 退出前停止自动轮询线程，避免后台线程残留/资源未释放
fn stop_poll_on_exit(app: &tauri::AppHandle) {
    let state = app.state::<AppState>();
    state.poll.running.store(false, Ordering::SeqCst);
    {
        let h = state.auto_poll.lock().unwrap().take();
        if let Some(h) = h {
            let _ = h.join();
        }
    }
}
